UBC-Rocket/Thrust-Vectoring/Mechanical/Gimbal_System/Hardware/McMaster/91290A121_Alloy Steel Socket Head Screw.SLDPRT

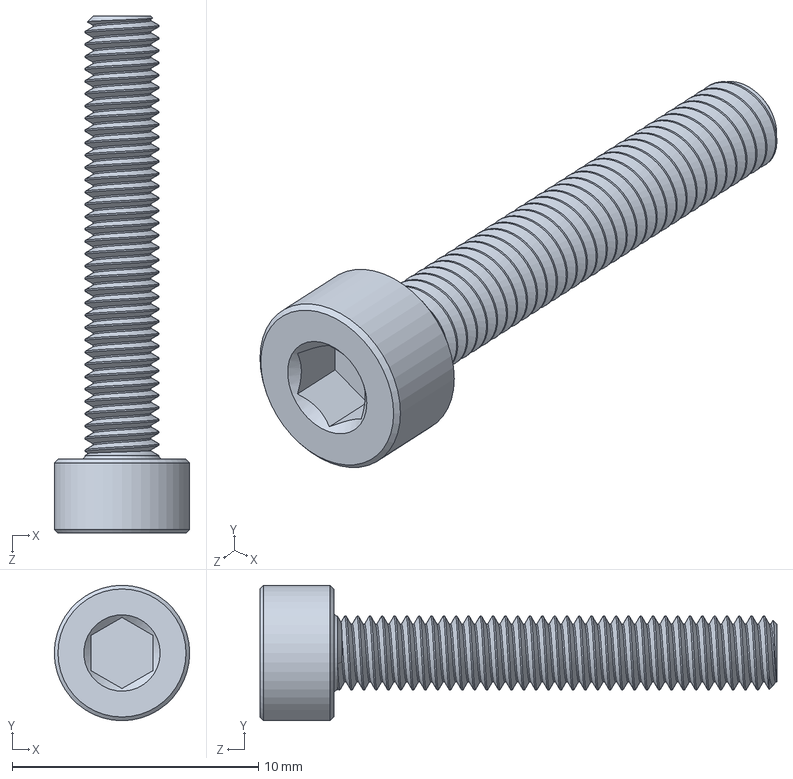
[picture p15: CAD file, 2024-07-03, last stored version]
Mechanical/Gimbal_System/Hardware/McMaster/91290A121_Alloy Steel Socket Head Screw.SLDPRT
5.50 x 5.50 x 21.0 mm
