UBC-Rocket/Thrust-Vectoring/Mechanical/Gimbal_System/Hardware/McMaster/93070A107_Alloy Steel Low-Profile Socket Head Screw.SLDPRT

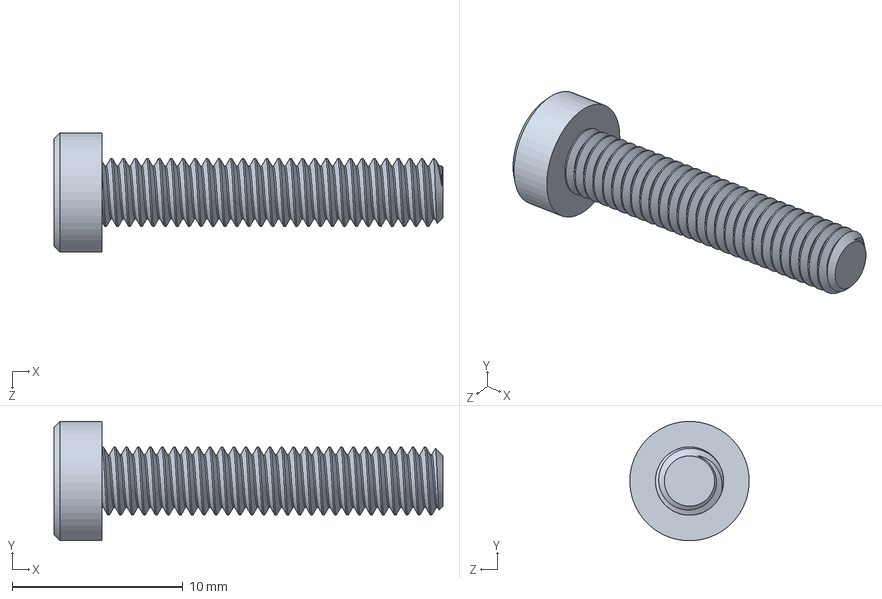
[picture p16: CAD file, 2024-07-03, last stored version]
Mechanical/Gimbal_System/Hardware/McMaster/93070A107_Alloy Steel Low-Profile Socket Head Screw.SLDPRT
22.8 x 6.99 x 7.00 mm
