UBC-Rocket/Thrust-Vectoring/Mechanical/Gimbal_System/Hardware/McMaster/93070A073_Alloy Steel Low-Profile Socket Head Screw.SLDPRT

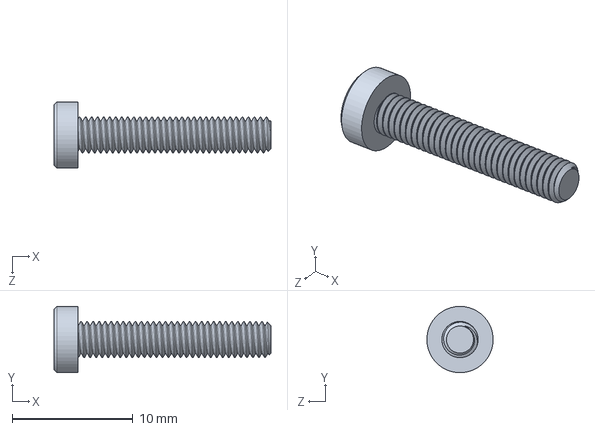
[picture p17: CAD file, 2024-07-03, last stored version]
Mechanical/Gimbal_System/Hardware/McMaster/93070A073_Alloy Steel Low-Profile Socket Head Screw.SLDPRT
18.0 x 5.49 x 5.50 mm
